0x0c/EmoT/Arduino/EmoT_firmware/emoji/1f4aa/1f4aa.gif

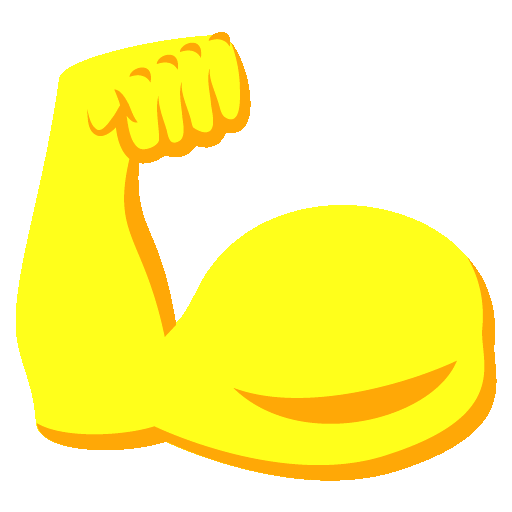
Arduino/EmoT_firmware/emoji/1f4aa/1f4aa.gif
