0x0c/EmoT/Arduino/EmoT_firmware/emoji/1f6ab/1f6ab.gif

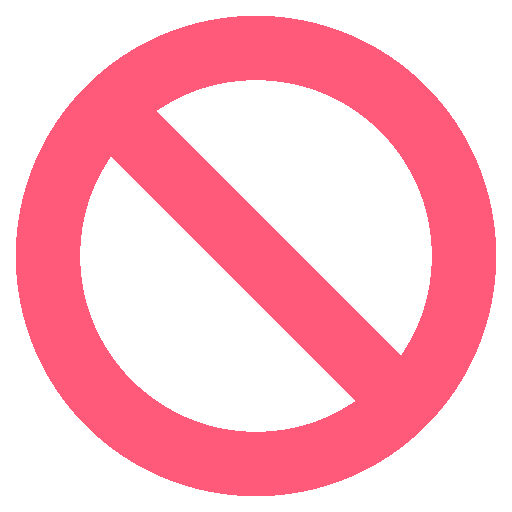
Arduino/EmoT_firmware/emoji/1f6ab/1f6ab.gif
