0x0c/EmoT/Arduino/EmoT_firmware/emoji/1f64f/1f64f.gif

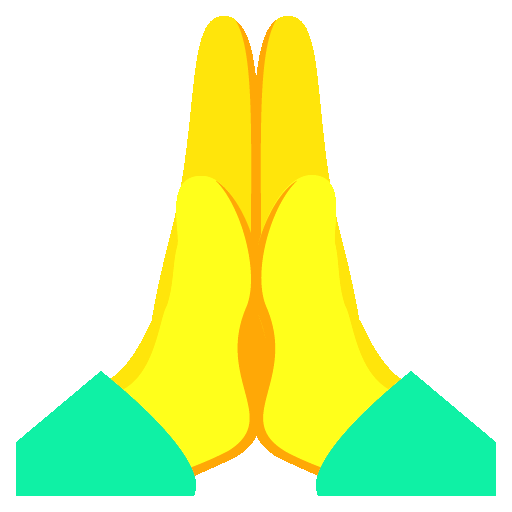
Arduino/EmoT_firmware/emoji/1f64f/1f64f.gif
