0x0c/EmoT/Arduino/EmoT_firmware/emoji/1f525/1f525.gif

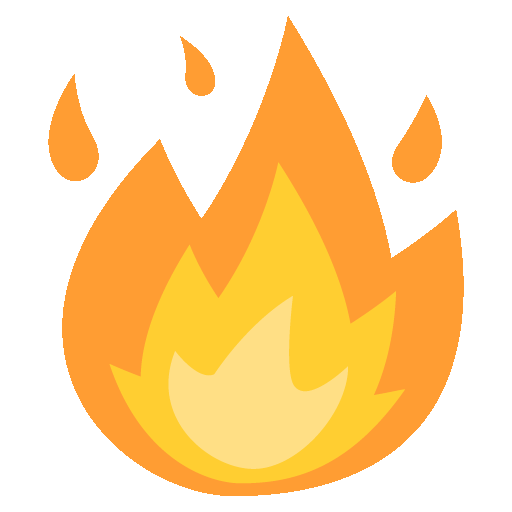
Arduino/EmoT_firmware/emoji/1f525/1f525.gif
