0x0c/EmoT/Arduino/EmoT_firmware/emoji/1f647/1f647.gif

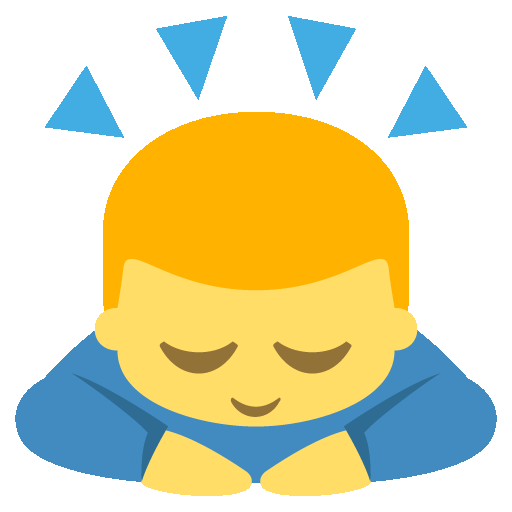
Arduino/EmoT_firmware/emoji/1f647/1f647.gif
