0x0c/EmoT/Arduino/EmoT_firmware/emoji/270c/270c.gif

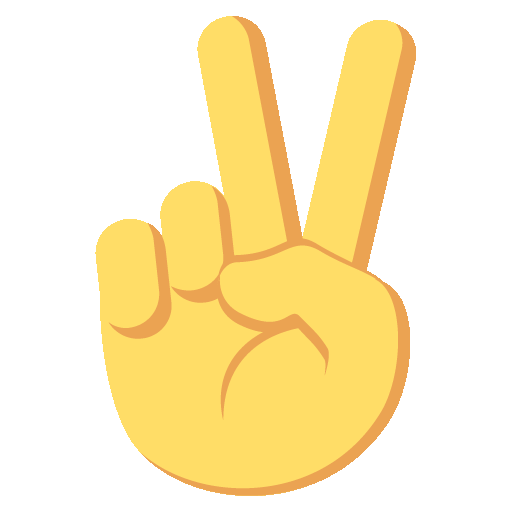
Arduino/EmoT_firmware/emoji/270c/270c.gif
