0x0c/EmoT/Arduino/EmoT_firmware/emoji/2705/2705.gif

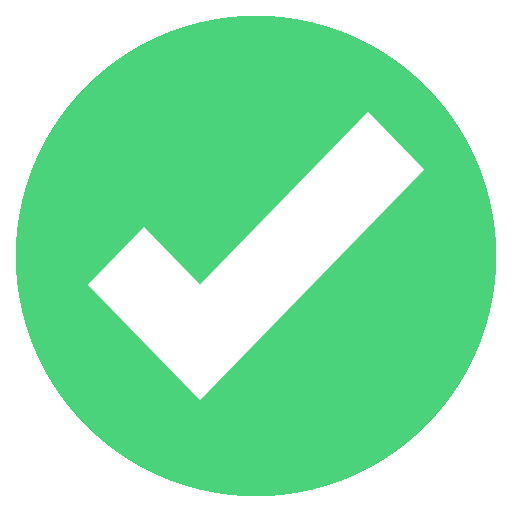
Arduino/EmoT_firmware/emoji/2705/2705.gif
