0x0c/EmoT/Arduino/EmoT_firmware/emoji/2753/2753.gif

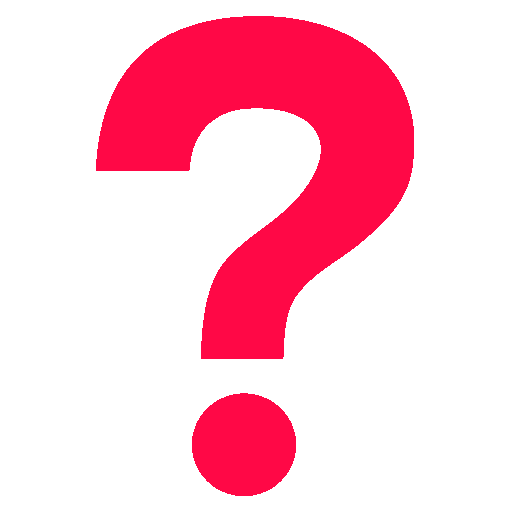
Arduino/EmoT_firmware/emoji/2753/2753.gif
