0x0c/EmoT/Arduino/EmoT_firmware/emoji/2757/2757.gif

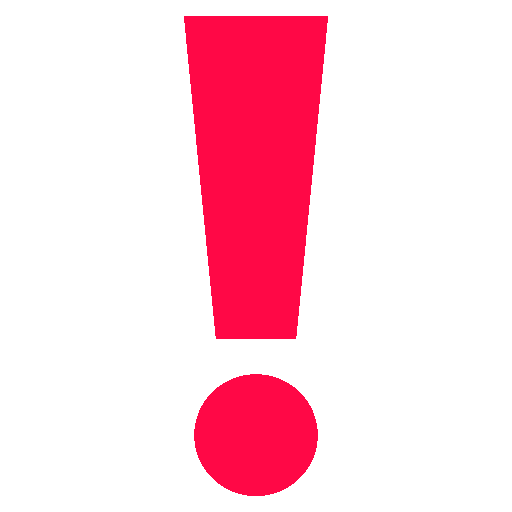
Arduino/EmoT_firmware/emoji/2757/2757.gif
