0x0c/EmoT/asset/photo/DSC04576.JPG

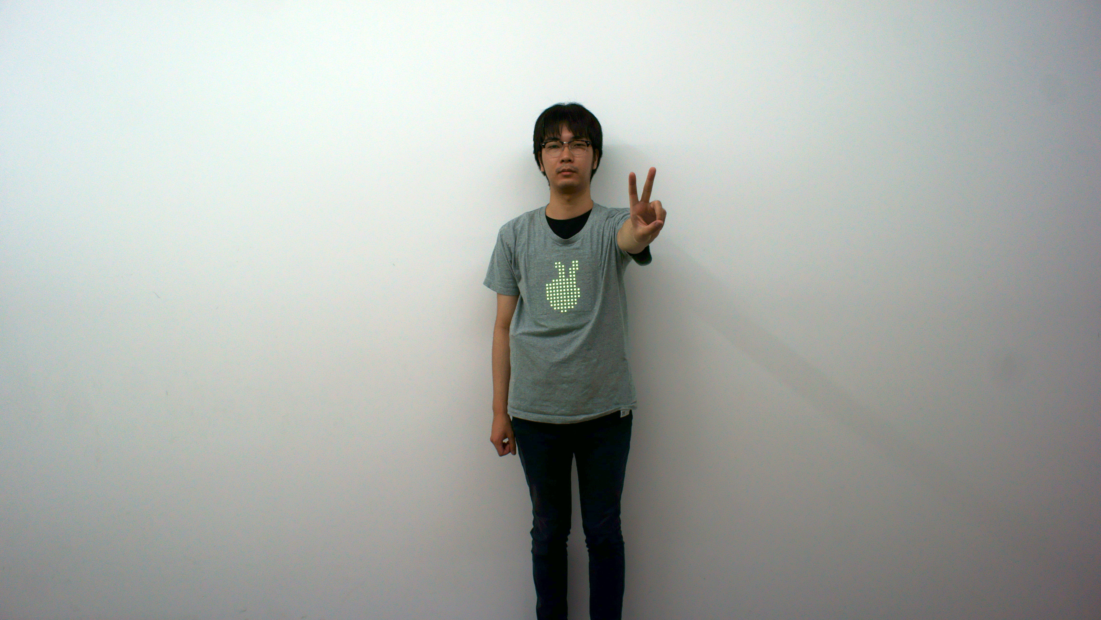
asset/photo/DSC04576.JPG
