0x0c/EmoT/asset/photo/DSC04578.JPG

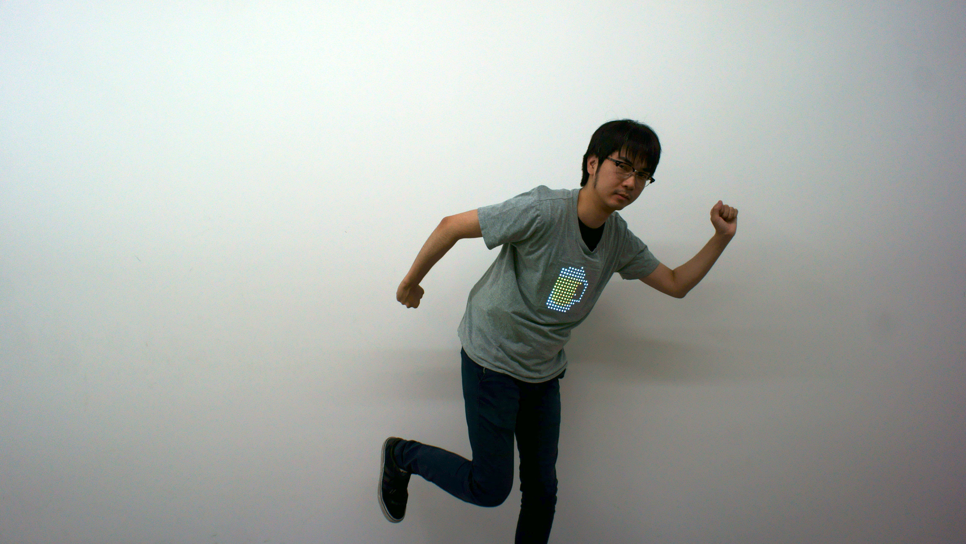
asset/photo/DSC04578.JPG
