0x0c/EmoT/asset/photo/DSC04587.JPG

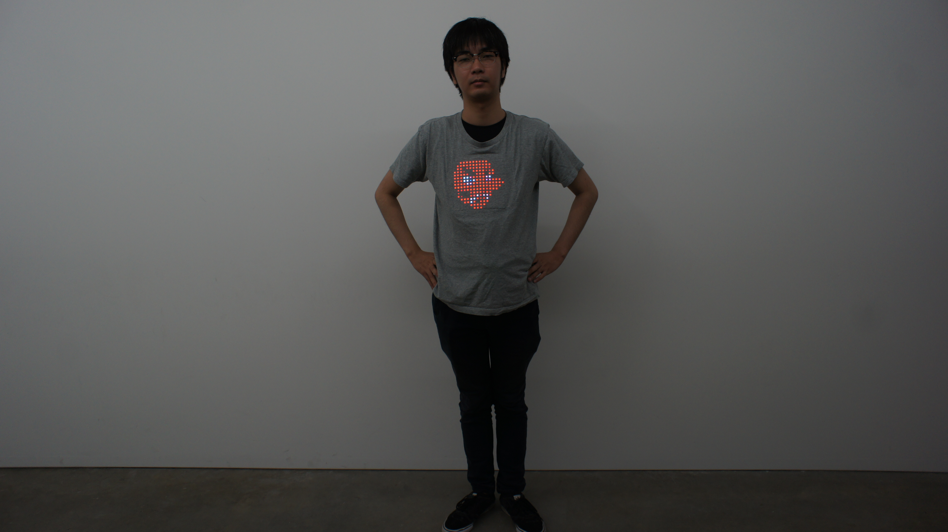
asset/photo/DSC04587.JPG
