0x0c/EmoT/asset/photo/DSC04588.JPG

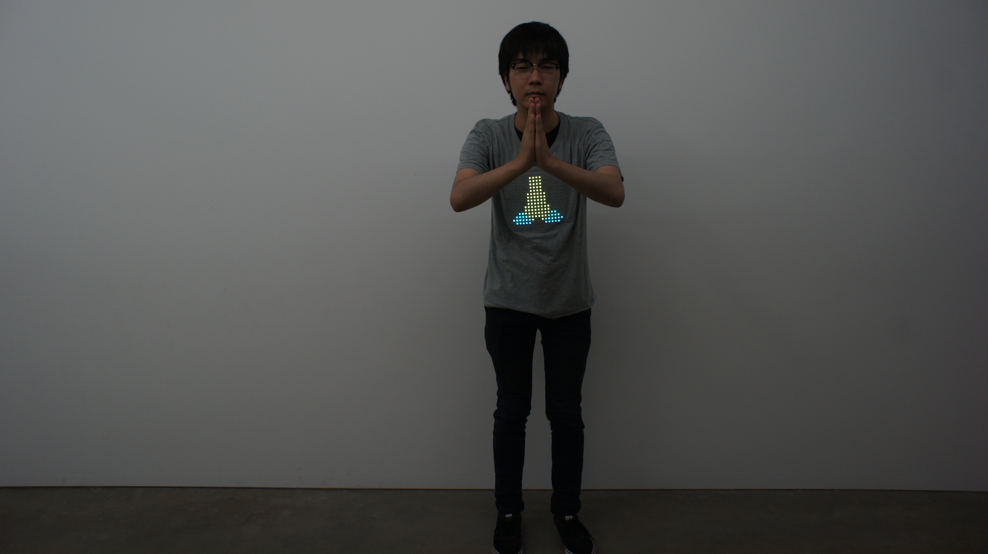
asset/photo/DSC04588.JPG
