0x0c/EmoT/asset/sensor_suit/IMG_9949.jpg

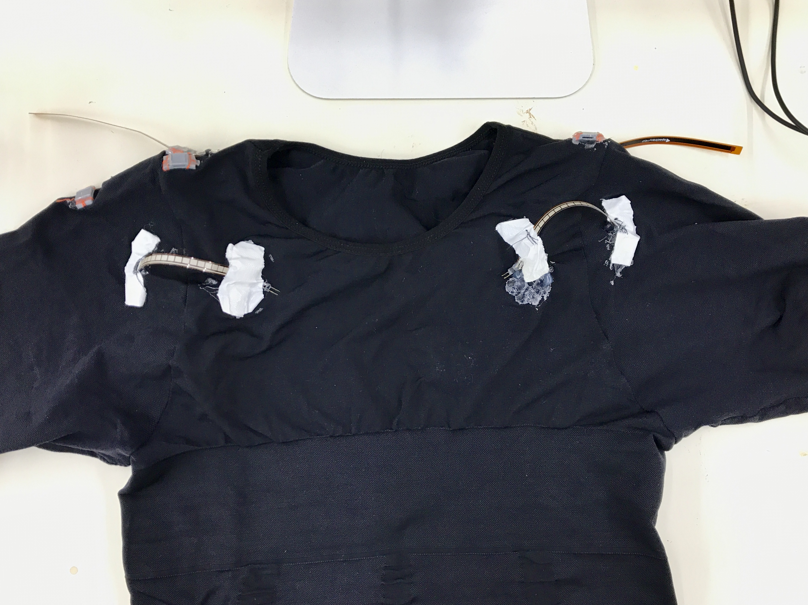
asset/sensor_suit/IMG_9949.jpg
