0x0c/EmoT/asset/sensor_suit/IMG_9950.jpg

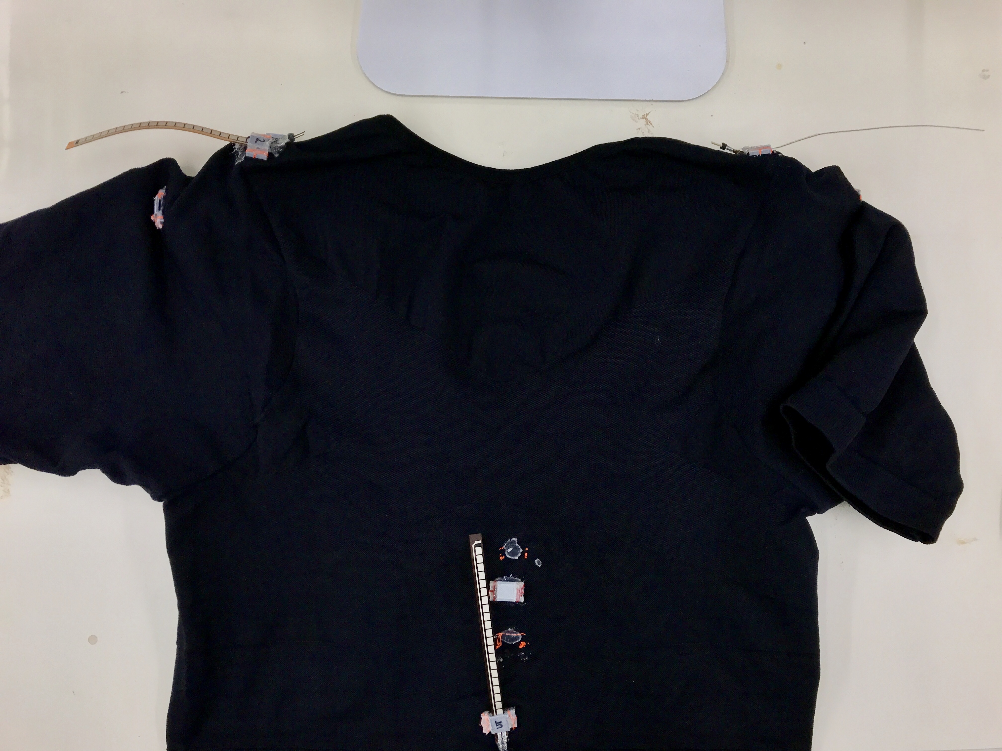
asset/sensor_suit/IMG_9950.jpg
