0x0c/EmoT/Arduino/EmoT_firmware/Emoticon.h

namespace Emoticon {
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
5,},{255,255,255,},{255,255,255,},{255,255,255,},{255,255,255,},{0,0,0,},{0,0,0,},{0,0,0,},},};
	unsigned char sushi[16][16][3] = {{{0,0,0,},{0,0,0,},{0,0,0,},{0,0,0,},{0,0,0,},{0,0,0,},{0,0,0,},{0,0,0,},{0,0,0,},{0,0,0,},{0,0,0,},{0,0,0,},{0,0,0,},{0,0,0,},{0,0,0,},{0,0,0,},},{{0,0,0,},{0,0,0,},{0,0,0,},{0,0,0,},{0,0,0,},{0,0,0,},{255,255,0,},{255,255,0,},{255,255,0,},{255,255,0,},{0,0,0,},{0,0,0,},{0,0,0,},{0,0,0,},{0,0,0,},{0,0,0,},},{{0,0,0,},{0,0,0,},{0,0,0,},{0,0,0,},{255,255,0,},{255,255,0,},{255,255,0,},{255,255,0,},{255,255,0,},{171,160,0,},{0,47,0,},{0,0,0,},{0,0,0,},{0,0,0,},{0,0,0,},{0,0,0,},},{{0,0,0,},{0,0,0,},{0,0,0,},{0,0,0,},{255,255,0,},{255,255,0,},{255,255,0,},{221,199,0,},{0,49,0,},{0,0,44,},{0,0,52,},{0,24,0,},{230,218,0,},{0,0,0,},{0,0,0,},{0,0,0,},},{{0,0,0,},{0,0,0,},{0,0,0,},{0,0,0,},{255,255,177,},{255,255,0,},{221,160,0,},{0,0,0,},{0,0,49,},{0,0,38,},{38,72,0,},{255,238,0,},{255,255,0,},{255,255,0,},{0,0,0,},{0,0,0,},},{{0,0,0,},{0,0,0,},{0,0,0,},{255,182,174,},{255,155,152,},{255,255,177,},{113,80,0,},{0,0,0,},{0,5,0,},{202,199,0,},{255,255,0,},{255,255,0,},{255,255,0,},{255,255,0,},{255,255,0,},{0,0,0,},},{{0,0,0,},{0,0,0,},{0,0,0,},{255,0,0,},{255,0,0,},{255,0,0,},{249,0,0,},{0,0,0,},{66,0,0,},{255,255,0,},{255,255,0,},{255,255,0,},{255,255,0,},{255,255,0,},{255,255,0,},{255,255,163,},},{{0,0,0,},{255,0,0,},{255,0,0,},{255,0,0,},{255,0,0,},{255,0,0,},{255,0,0,},{255,0,0,},{166,0,0,},{255,255,0,},{255,255,0,},{255,255,0,},{255,255,0,},{255,255,0,},{255,255,249,},{0,0,0,},},{{255,0,0,},{255,0,0,},{255,0,0,},{255,11,0,},{255,0,0,},{255,0,0,},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
,{0,0,0,},{0,0,0,},{0,0,0,},{0,0,0,},{0,0,0,},{255,255,8,},{255,255,8,},{0,0,0,},{0,0,0,},{0,0,0,},{0,0,0,},{0,0,0,},{0,0,0,},{0,0,0,},},};
	unsigned char sad2[16][16][3] = {{{0,0,0,},{0,0,0,},{0,0,0,},{0,0,0,},{0,0,0,},{0,0,0,},{0,0,0,},{255,255,8,},{255,255,8,},{0,0,0,},{0,0,0,},{0,0,0,},{0,0,0,},{0,0,0,},{0,0,0,},{0,0,0,},},{{0,0,0,},{0,0,0,},{0,0,0,},{0,0,0,},{255,255,8,},{255,255,8,},{255,255,8,},{255,255,8,},{255,255,8,},{255,255,8,},{255,255,8,},{255,255,8,},{0,0,0,},{0,0,0,},{0,0,0,},{0,0,0,},},{{0,0,0,},{0,0,0,},{0,0,0,},{255,255,8,},{255,255,11,},{255,255,11,},{255,255,8,},{255,255,8,},{255,255,8,},{255,255,8,},{255,255,11,},{255,255,11,},{255,255,11,},{0,0,0,},{0,0,0,},{0,0,0,},},{{0,0,0,},{0,0,0,},{255,255,8,},{255,255,0,},{255,255,0,},{255,255,0,},{255,255,8,},{255,255,8,},{255,255,8,},{255,255,8,},{255,255,0,},{255,255,0,},{255,255,0,},{255,255,8,},{0,0,0,},{0,0,0,},},{{0,0,0,},{255,255,8,},{255,255,0,},{255,194,0,},{255,227,0,},{255,255,0,},{255,255,5,},{255,255,8,},{255,255,8,},{255,255,5,},{255,255,0,},{255,232,0,},{255,194,0,},{255,252,0,},{255,255,8,},{0,0,0,},},{{0,0,0,},{255,255,8,},{255,255,0,},{255,255,88,},{255,255,202,},{255,255,166,},{255,255,36,},{255,255,5,},{255,255,5,},{255,255,36,},{255,255,166,},{255,255,202,},{255,255,91,},{255,255,0,},{255,255,8,},{0,0,0,},},{{0,0,0,},{255,255,2,},{255,255,99,},{255,255,238,},{146,105,38,},{224,191,138,},{255,255,218,},{255,255,16,},{255,255,16,},{255,255,218,},{221,188,135,},{149,108,41,},{255,255,241,},{255,255,97,},{255,255,2,},{0,0,0,},},{{255,255,8,},{255,255,2,},{255,255,199,},{152,110,44,},{52,0,0,},{160,121,55,},{255,255,232,},{255,255,55,},{255,255,55,},{255,255,227,},{36,0,0,},{127,80,5,},{210,177,124,},{255,255,194,},{255,255,2,},{255,255,8,},},{{255,255,8,},{255,255,2,},{255,255,157,},{255,255,252,},{255,255,252,},{177,138,80,},{255,255,243,},{255,255,38,},{255,255,38,},{255,255,255,},{255,255,255,},{232,202,155,},{243,213,163,},{255,255,160,},{255,255,2,},{255,255,8,},},{{0,0,0,},{255,255,5,},{255,255,30,},{255,255,255,},{210,255,255,},{255,255,255,},{255,255,119,},{255,255,5,},{255,255,5,},{255,255,121,},{255,255,255,},{255,255,255,},{255,255,213,},{255,255,36,},{255,255,5,},{0,0,0,},},{{0,0,0,},{255,255,5,},{255,255,22,},{133,249,255,},{16,218,255,},{255,255,149,},{255,255,0,},{255,255,0,},{255,255,0,},{255,255,5,},{255,255,36,},{255,255,55,},{255,255,16,},{255,255,5,},{255,255,8,},{0,0,0,},},{{0,0,0,},{255,255,0,},{255,255,119,},{16,216,255,},{0,213,255,},{91,213,255,},{169,102,0,},{121,47,0,},{121,47,0,},{174,97,0,},{255,255,0,},{255,255,5,},{255,255,8,},{255,255,8,},{255,255,8,},{0,0,0,},},{{0,0,0,},{0,0,0,},{138,252,255,},{0,213,255,},{2,213,255,},{8,199,255,},{207,180,19,},{255,246,0,},{255,243,0,},{255,185,0,},{255,255,0,},{255,255,8,},{255,255,8,},{255,255,8,},{0,0,0,},{0,0,0,},},{{0,0,0,},{0,0,0,},{2,213,255,},{2,213,255,},{2,213,255,},{13,216,255,},{255,255,113,},{255,255,5,},{255,255,11,},{255,255,11,},{255,255,8,},{255,255,8,},{255,255,8,},{0,0,0,},{0,0,0,},{0,0,0,},},{{0,0,0,},{0,0,0,},{0,0,0,},{2,213,255,},{0,213,255,},{72,232,255,},{255,255,55,},{255,255,5,},{255,255,8,},{255,255,8,},{255,255,8,},{255,255,8,},{0,0,0,},{0,0,0,},{0,0,0,},{0,0,0,},},{{0,0,0,},{0,0,0,},{0,0,0,},{0,0,0,},{0,213,255,},{0,0,0,},{0,0,0,},{255,255,8,},{255,255,8,},{0,0,0,},{0,0,0,},{0,0,0,},{0,0,0,},{0,0,0,},{0,0,0,},{0,0,0,},},};
	unsigned char vsign[16][16][3] = {{{0,0,0,},{0,0,0,},{0,0,0,},{0,0,0,},{0,0,0,},{0,0,0,},{0,0,0,},{0,0,0,},{0,0,0,},{0,0,0,},{0,0,0,},{0,0,0,},{0,0,0,},{0,0,0,},{0,0,0,},{0,0,0,},},{{0,0,0,},{0,0,0,},{0,0,0,},{255,255,0,},{255,255,8,},{0,0,0,},{0,0,0,},{0,0,0,},{255,255,0,},{255,255,8,},{0,0,0,},{0,0,0,},{0,0,0,},{0,0,0,},{0,0,0,},{0,0,0,},},{{0,0,0,},{0,0,0,},{0,0,0,},{255,246,0,},{255,255,8,},{0,0,0,},{0,0,0,},{255,216,0,},{255,255,0,},{255,255,8,},{0,0,0,},{0,0,0,},{0,0,0,},{0,0,0,},{0,0,0,},{0,0,0,},},{{0,0,0,},{0,0,0,},{0,0,0,},{255,224,0,},{255,255,2,},{255,255,8,},{0,0,0,},{255,235,0,},{255,255,5,},{0,0,0,},{0,0,0,},{0,0,0,},{0,0,0,},{0,0,0,},{0,0,0,},{0,0,0,},},{{0,0,0,},{0,0,0,},{0,0,0,},{0,0,0,},{255,255,0,},{255,255,8,},{0,0,0,},{255,255,0,},{255,255,8,},{0,0,0,},{0,0,0,},{0,0,0,},{0,0,0,},{0,0,0,},{0,0,0,},{0,0,0,},},{{0,0,0,},{0,0,0,},{0,0,0,},{0,0,0,},{255,255,0,},{255,255,11,},{0,0,0,},{255,255,0,},{255,255,8,},{0,0,0,},{0,0,0,},{0,0,0,},{0,0,0,},{0,0,0,},{0,0,0,},{0,0,0,},},{{0,0,0,},{0,0,0,},{0,0,0,},{0,0,0,},{255,255,0,},{255,255,8,},{255,255,0,},{255,255,0,},{255,255,0,},{255,255,0,},{255,255,8,},{0,0,0,},{0,0,0,},{0,0,0,},{0,0,0,},{0,0,0,},},{{0,0,0,},{0,0,0,},{0,0,0,},{0,0,0,},{255,227,0,},{255,255,0,},{255,255,0,},{255,255,0,},{255,255,0,},{255,255,0,},{255,255,2,},{255,255,0,},{255,255,8,},{0,0,0,},{0,0,0,},{0,0,0,},},{{0,0,0,},{0,0,0,},{0,0,0,},{0,0,0,},{255,255,0,},{255,255,0,},{255,255,8,},{255,255,2,},{255,255,0,},{255,255,0,},{255,255,0,},{255,255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
,0,0,},{0,0,0,},{0,0,0,},{0,0,0,},},{{0,0,0,},{0,0,0,},{0,0,0,},{0,0,0,},{0,0,0,},{0,0,0,},{0,0,0,},{255,255,8,},{255,255,8,},{0,0,0,},{0,0,0,},{0,0,0,},{0,0,0,},{0,0,0,},{0,0,0,},{0,0,0,},},};
	unsigned char sorry[16][16][3] = {{{0,0,0,},{0,0,0,},{0,0,0,},{0,0,0,},{0,0,0,},{0,0,0,},{0,0,0,},{0,0,0,},{0,0,0,},{0,0,0,},{0,0,0,},{0,0,0,},{0,0,0,},{0,0,0,},{0,0,0,},{0,0,0,},},{{0,0,0,},{0,0,0,},{0,0,0,},{0,0,0,},{0,0,0,},{0,202,255,},{0,202,255,},{0,0,0,},{0,0,0,},{0,202,255,},{0,202,255,},{0,0,0,},{0,0,0,},{0,0,0,},{0,0,0,},{0,0,0,},},{{0,0,0,},{0,0,0,},{0,0,0,},{0,0,0,},{0,0,0,},{0,0,0,},{0,0,0,},{0,0,0,},{0,0,0,},{0,0,0,},{0,0,0,},{0,0,0,},{0,0,0,},{0,0,0,},{0,0,0,},{0,0,0,},},{{0,0,0,},{0,0,0,},{0,202,255,},{0,0,0,},{0,0,0,},{0,0,0,},{0,0,0,},{0,0,0,},{0,0,0,},{0,0,0,},{0,0,0,},{0,0,0,},{0,0,0,},{0,202,255,},{0,0,0,},{0,0,0,},},{{0,0,0,},{0,0,0,},{0,0,0,},{0,0,0,},{0,0,0,},{255,218,0,},{255,218,0,},{255,218,0,},{255,218,0,},{255,218,0,},{255,218,0,},{0,0,0,},{0,0,0,},{0,0,0,},{0,0,0,},{0,0,0,},},{{0,0,0,},{0,0,0,},{0,0,0,},{0,0,0,},{255,218,0,},{255,218,0,},{255,218,0,},{255,218,0,},{255,218,0,},{255,218,0,},{255,218,0,},{255,218,0,},{0,0,0,},{0,0,0,},{0,0,0,},{0,0,0,},},{{0,0,0,},{0,0,0,},{0,0,0,},{255,218,0,},{255,218,0,},{255,218,0,},{255,218,0,},{255,218,0,},{255,218,0,},{255,218,0,},{255,218,0,},{255,218,0,},{255,218,0,},{0,0,0,},{0,0,0,},{0,0,0,},},{{0,0,0,},{0,0,0,},{0,0,0,},{255,221,0,},{255,221,0,},{255,216,0,},{255,216,0,},{255,218,0,},{255,218,0,},{255,216,0,},{255,216,0,},{255,221,0,},{255,221,0,},{0,0,0,},{0,0,0,},{0,0,0,},},{{0,0,0,},{0,0,0,},{0,0,0,},{255,246,0,},{255,255,0,},{255,255,0,},{255,241,0,},{255,230,0,},{255,230,0,},{255,241,0,},{255,255,0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
0,0,},{0,0,0,},{0,0,0,},{0,0,0,},{0,0,0,},{0,0,0,},},};
	unsigned char notgood[16][16][3] = {{{0,0,0,},{0,0,0,},{0,0,0,},{0,0,0,},{0,0,0,},{0,0,0,},{255,255,0,},{255,255,0,},{255,255,0,},{255,255,0,},{0,0,0,},{0,0,0,},{0,0,0,},{0,0,0,},{0,0,0,},{0,0,0,},},{{0,0,0,},{0,0,0,},{0,0,0,},{0,0,0,},{0,0,0,},{255,255,0,},{255,255,0,},{255,255,0,},{255,255,0,},{255,255,0,},{255,255,44,},{0,0,0,},{0,0,0,},{0,0,0,},{0,0,0,},{0,0,0,},},{{0,0,0,},{0,0,0,},{0,0,0,},{255,255,0,},{255,255,0,},{255,255,0,},{255,255,0,},{255,255,0,},{255,255,0,},{255,255,0,},{255,255,0,},{255,255,63,},{255,255,94,},{0,0,0,},{0,0,0,},{0,0,0,},},{{0,0,0,},{0,0,0,},{255,255,0,},{255,255,0,},{255,255,0,},{255,255,0,},{255,255,0,},{255,255,0,},{255,255,0,},{255,255,0,},{255,255,0,},{255,255,0,},{255,255,49,},{255,255,88,},{0,0,0,},{0,0,0,},},{{0,0,0,},{255,255,0,},{255,255,0,},{255,255,0,},{255,246,0,},{255,232,0,},{255,255,0,},{255,255,0,},{255,255,0,},{255,255,0,},{255,232,0,},{255,246,0,},{255,255,0,},{255,255,19,},{0,0,0,},{0,0,0,},},{{0,0,0,},{255,255,0,},{255,255,0,},{255,243,0,},{11,0,0,},{0,0,0,},{255,185,0,},{255,255,0,},{255,255,0,},{255,185,0,},{0,0,0,},{11,0,0,},{255,243,0,},{255,255,0,},{255,255,0,},{0,0,0,},},{{255,243,0,},{255,255,0,},{255,255,0,},{255,227,0,},{0,0,0,},{0,0,0,},{255,155,0,},{255,255,0,},{255,255,0,},{255,155,0,},{0,0,0,},{0,0,0,},{255,227,0,},{255,255,0,},{255,255,0,},{255,255,0,},},{{255,238,0,},{255,255,0,},{255,255,0,},{255,255,0,},{255,177,0,},{249,149,0,},{255,255,0,},{255,255,0,},{255,255,0,},{255,255,0,},{249,149,0,},{255,177,0,},{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
}
