0x0c/EmoT/Arduino/EmoT_firmware/PoseDetector.h

class PoseDetector {

  public:
 enum Pose {question,vsign,arm,standing,beer,sushi};
 static double classify(int i[5])
     {

    double p = -1;
    p = PoseDetector::N3bb25aa634(i);
    return p;
  }
  static double N3bb25aa634(int i[5]) {
    double p = -1;
    if (i[0] == 0) {
      p = 0;
      } else if (i[0] <= 11708.0) {
    p = PoseDetector::N3a5d66e835(i);
    } else if (i[0] > 11708.0) {
    p = PoseDetector::N567172fc43(i);
    } 
    return p;
  }
  static double N3a5d66e835(int i[5]) {
    double p = -1;
    if (i[1] == 0) {
      p = 3;
    } else if (i[1] <= 9112.0) {
      p = 3;
    } else if (i[1] > 9112.0) {
    p = PoseDetector::N4a0f274736(i);
    } 
    return p;
  }
  static double N4a0f274736(int i[5]) {
    double p = -1;
    if (i[0] == 0) {
      p = 1;
    } else if (i[0] <= 10974.0) {
    p = PoseDetector::N28dbcc4d37(i);
    } else if (i[0] > 10974.0) {
    p = PoseDetector::N32a6d5b42(i);
    } 
    return p;
  }
  static double N28dbcc4d37(int i[5]) {
    double p = -1;
    if (i[1] == 0) {
      p = 1;
    } else if (i[1] <= 9974.0) {
      p = 1;
    } else if (i[1] > 9974.0) {
    p = PoseDetector::N7641e82f38(i);
    } 
    return p;
  }
  static double N7641e82f38(int i[5]) {
    double p = -1;
    if (i[0] == 0) {
      p = 1;
    } else if (i[0] <= 10889.0) {
      p = 1;
    } else if (i[0] > 10889.0) {
    p = PoseDetector::N60f2a25039(i);
    } 
    return p;
  }
  static double N60f2a25039(int i[5]) {
    double p = -1;
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
      p = 4;
    } else if (i[3] > 12142.0) {
      p = 2;
    } 
    return p;
  }
  static double N87ddeea50(int i[5]) {
    double p = -1;
    if (i[0] == 0) {
      p = 4;
    } else if (i[0] <= 12962.0) {
      p = 4;
    } else if (i[0] > 12962.0) {
      p = 2;
    } 
    return p;
  }
}
;
