0x0c/EmoT/Arduino/EmoT_LED_Test/PoseDetector.h

// class PoseDetector {

//   public:
//         enum Pose {
//       question,vsign,arm,standing,beer,sushi
//     };
//    static double classify(int i[5])
//      {

//     double p = -1;
//     p = PoseDetector::N139c75e935(i);
//     return p;
//   }
//   static double N139c75e935(int i[5]) {
//     double p = -1;
//     if (i[3] == 0) {
//       p = 2;
//     } else if (i[3] <= 11527.0) {
//     p = PoseDetector::N5011e0e36(i);
//     } else if (i[3] > 11527.0) {
//     p = PoseDetector::Nc5c2bb337(i);
//     } 
//     return p;
//   }
//   static double N5011e0e36(int i[5]) {
//     double p = -1;
//     if (i[3] == 0) {
//       p = 5;
//     } else if (i[3] <= 10234.0) {
//       p = 5;
//     } else if (i[3] > 10234.0) {
//       p = 2;
//     } 
//     return p;
//   }
//   static double Nc5c2bb337(int i[5]) {
//     double p = -1;
//     if (i[1] == 0) {
//       p = 3;
//     } else if (i[1] <= 8128.0) {
//     p = PoseDetector::N7738fb1b38(i);
//     } else if (i[1] > 8128.0) {
//     p = PoseDetector::N3dede6c339(i);
//     } 
//     return p;
//   }
//   static double N7738fb1b38(int i[5]) {
//     double p = -1;
//     if (i[1] == 0) {
//       p = 4;
//     } else if (i[1] <= 6684.0) {
//       p = 4;
//     } else if (i[1] > 6684.0) {
//       p = 3;
//     } 
//     return p;
//   }
//   static double N3dede6c339(int i[5]) {
//     double p = -1;
//     if (i[4] == 0) {
//       p = 1;
//     } else if (i[4] <= 11985.0) {
//     p = PoseDetector::N4dc92bf840(i);
//     } else if (i[4] > 11985.0) {
//     p = PoseDetector::N3d83b5a155(i);
//     } 
//     return p;
//   }
//   static double N4dc92bf840(int i[5]) {
//     double p = -1;
//     if (i[4] == 0) {
//       p = 1;
//     } else if (i[4] <= 11617.0) {
//       p = 1;
//     } else if (i[4] > 11617.0) {
//     p = PoseDetector::N5265cead41(i);
//     } 
//     return p;
//   }
//   static double N5265cead41(int i[5]) {
//     double p = -1;
//     if (i[1] == 0) {
//       p = 1;
//     } else if (i[1] <= 8833.0) {
//     p = PoseDetector::N19e3ea1e42(i);
//     } else if (i[1] > 8833.0) {
//     p = PoseDetector::N427fb1d345(i);
//     } 
//     return p;
//   }
//   static double N19e3ea1e42(int i[5]) {
//     double p = -1;
//     if (i[2] == 0) {
//       p = 1;
//     } else if (i[2] <= 12366.0) {
//     p = PoseDetector::N421f64d943(i);
//     } else if (i[2] > 12366.0) {
//       p = 0;
//     } 
//     return p;
//   }
//   static double N421f64d943(int i[5]) {
//     double p = -1;
//     if (i[0] == 0) {
//       p = 1;
//     } else if (i[0] <= 11174.0) {
//       p = 1;
//     } else if (i[0] > 11174.0) {
//     p = PoseDetector::N1b16047944(i);
//     } 
//     return p;
//   }
//   static double N1b16047944(int i[5]) {
//     double p = -1;
//     if (i[1] == 0) {
//       p = 1;
//     } else if (i[1] <= 8697.0) {
//       p = 1;
//     } else if (i[1] > 8697.0) {
//       p = 0;
//     } 
//     return p;
//   }
//   static double N427fb1d345(int i[5]) {
//     double p = -1;
//     if (i[0] == 0) {
//       p = 1;
//     } else if (i[0] <= 11174.0) {
//     p = PoseDetector::N4d73b5c046(i);
//     } else if (i[0] > 11174.0) {
//       p = 0;
//     } 
//     return p;
//   }
//   static double N4d73b5c046(int i[5]) {
//     double p = -1;
//     if (i[1] == 0) {
//       p = 1;
//     } else if (i[1] <= 9278.0) {
//     p = PoseDetector::N67a177f947(i);
//     } else if (i[1] > 9278.0) {
//     p = PoseDetector::N338669ac54(i);
//     } 
//     return p;
//   }
//   static double N67a177f947(int i[5]) {
//     double p = -1;
//     if (i[2] == 0) {
//       p = 1;
//     } else if (i[2] <= 12398.0) {
//     p = PoseDetector::N19cbb19648(i);
//     } else if (i[2] > 12398.0) {
//     p = PoseDetector::N5ea0f39052(i);
//     } 
//     return p;
//   }
//   static double N19cbb19648(int i[5]) {
//     double p = -1;
//     if (i[4] == 0) {
//       p = 1;
//     } else if (i[4] <= 11861.0) {
//     p = PoseDetector::Nbf7fc1549(i);
//     } else if (i[4] > 11861.0) {
//     p = PoseDetector::N45c6ccd650(i);
//     } 
//     return p;
//   }
//   static double Nbf7fc1549(int i[5]) {
//     double p = -1;
//     if (i[3] == 0) {
//       p = 1;
//     } else if (i[3] <= 13065.0) {
//       p = 1;
//     } else if (i[3] > 13065.0) {
//       p = 0;
//     } 
//     return p;
//   }
//   static double N45c6ccd650(int i[5]) {
//     double p = -1;
//     if (i[0] == 0) {
//       p = 1;
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
      p = 1;
    } else if (i[4] > 11648.0) {
      p = 0;
    } 
    return p;
  }
  static double N16f3233597(int i[5]) {
    double p = -1;
    if (i[1] == 0) {
      p = 1;
    } else if (i[1] <= 8629.0) {
      p = 1;
    } else if (i[1] > 8629.0) {
      p = 0;
    } 
    return p;
  }
};
