0x0c/EmoT/Arduino/EmoT_SensorTest/PoseDetector.h

namespace m2d {
class PoseDetector {
  public:
    enum Pose {
      question,
      exclamation,
      arm,
      surprise,
      anxious,
      vsign,
      tengu,
      pray,
      standing
    };
    static double detect(int i[5]) {
      double p = -1;
      p = PoseDetector::N69e2c341264(i);
      return p;
    }
    static double N69e2c341264(int i[5]) {
      double p = -1;
      if (i[2] == 0) {
        p = 1;
      } else if (i[2] <= 10208.0) {
        p = PoseDetector::N268116b6265(i);
      } else if (i[2] > 10208.0) {
        p = PoseDetector::N4fd1b3bc281(i);
      }
      return p;
    }
    static double N268116b6265(int i[5]) {
      double p = -1;
      if (i[4] == 0) {
        p = 8;
      } else if (i[4] <= 10367.0) {
        p = PoseDetector::N64fa1a79266(i);
      } else if (i[4] > 10367.0) {
        p = PoseDetector::N5a808671279(i);
      }
      return p;
    }
    static double N64fa1a79266(int i[5]) {
      double p = -1;
      if (i[0] == 0) {
        p = 8;
      } else if (i[0] <= 10287.0) {
        p = PoseDetector::N5fe031b9267(i);
      } else if (i[0] > 10287.0) {
        p = PoseDetector::N63c4068b275(i);
      }
      return p;
    }
    static double N5fe031b9267(int i[5]) {
      double p = -1;
      if (i[4] == 0) {
        p = 8;
      } else if (i[4] <= 9745.0) {
        p = PoseDetector::N77e099db268(i);
      } else if (i[4] > 9745.0) {
        p = PoseDetector::N4ee1d6a3272(i);
      }
      return p;
    }
    static double N77e099db268(int i[5]) {
      double p = -1;
      if (i[2] == 0) {
        p = 8;
      } else if (i[2] <= 9922.0) {
        p = PoseDetector::N3a953659269(i);
      } else if (i[2] > 9922.0) {
        p = 2;
      }
      return p;
    }
    static double N3a953659269(int i[5]) {
      double p = -1;
      if (i[1] == 0) {
        p = 5;
      } else if (i[1] <= 6196.0) {
        p = PoseDetector::N1a232b1b270(i);
      } else if (i[1] > 6196.0) {
        p = 8;
      }
      return p;
    }
    static double N1a232b1b270(int i[5]) {
      double p = -1;
      if (i[1] == 0) {
        p = 5;
      } else if (i[1] <= 6145.0) {
        p = 5;
      } else if (i[1] > 6145.0) {
        p = PoseDetector::N7ae30704271(i);
      }
      return p;
    }
    static double N7ae30704271(int i[5]) {
      double p = -1;
      if (i[1] == 0) {
        p = 5;
      } else if (i[1] <= 6179.0) {
        p = 5;
      } else if (i[1] > 6179.0) {
        p = 8;
      }
      return p;
    }
    static double N4ee1d6a3272(int i[5]) {
      double p = -1;
      if (i[1] == 0) {
        p = 5;
      } else if (i[1] <= 6332.0) {
        p = 5;
      } else if (i[1] > 6332.0) {
        p = PoseDetector::N4cd28fca273(i);
      }
      return p;
    }
    static double N4cd28fca273(int i[5]) {
      double p = -1;
      if (i[4] == 0) {
        p = 8;
      } else if (i[4] <= 9846.0) {
        p = 8;
      } else if (i[4] > 9846.0) {
        p = PoseDetector::N13de3e2d274(i);
      }
      return p;
    }
    static double N13de3e2d274(int i[5]) {
      double p = -1;
      if (i[0] == 0) {
        p = 7;
      } else if (i[0] <= 9897.0) {
        p = 7;
      } else if (i[0] > 9897.0) {
        p = 5;
      }
      return p;
    }
    static double N63c4068b275(int i[5]) {
      double p = -1;
      if (i[4] == 0) {
        p = 4;
      } else if (i[4] <= 9720.0) {
        p = PoseDetector::N5a89c2d8276(i);
      } else if (i[4] > 9720.0) {
        p = PoseDetector::Na572158277(i);
      }
      return p;
    }
    static double N5a89c2d8276(int i[5]) {
      double p = -1;
      if (i[1] == 0) {
        p = 4;
      } else if (i[1] <= 6506.0) {
        p = 4;
      } else if (i[1] > 6506.0) {
        p = 2;
      }
      return p;
    }
    static double Na572158277(int i[5]) {
      double p = -1;
      if (i[2] == 0) {
        p = 4;
      } else if (i[2] <= 10000.0) {
        p = PoseDetector::N5e4e1db5278(i);
      } else if (i[2] > 10000.0) {
        p = 4;
      }
      return p;
    }
    static double N5e4e1db5278(int i[5]) {
      double p = -1;
      if (i[1] == 0) {
        p = 5;
      } else if (i[1] <= 6298.0) {
        p = 5;
      } else if (i[1] > 6298.0) {
        p = 4;
      }
      return p;
    }
    static double N5a808671279(int i[5]) {
      double p = -1;
      if (i[1] == 0) {
        p = 1;
      } else if (i[1] <= 6213.0) {
        p = 1;
      } else if (i[1] > 6213.0) {
        p = PoseDetector::N2bfa9322280(i);
      }
      return p;
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
      }
      return p;
    }
    static double N211e635a385(int i[5]) {
      double p = -1;
      if (i[1] == 0) {
        p = 3;
      } else if (i[1] <= 6524.0) {
        p = 3;
      } else if (i[1] > 6524.0) {
        p = 4;
      }
      return p;
    }
};
}
